rabaugart/helclock/Software/clock3/c3/color.py

import functools
from enum import Enum

class RGB(Enum):
    rot = 0
    grün = 1
    blau = 2

class Color:
    def __init__(self,r,g,b):
        self.b = bytearray([r,g,b])
    def set(self,rgb,value):
        self.b[rgb.value] = int(value) & 0xff
    def __eq__(self,o):
        if isinstance(o,Color):
            return self.b == o.b
        return False
    def __mul__(self,fac):
        nfac = max(min(float(fac),1.0),0.0)
        return Color(*list(int(i*nfac) for i in self.b))
    def copy(self):
        return Color(self.b[0],self.b[1],self.b[2])
    def __hash__(self):
        return hash(self.b.hex())
    def msg_dict(self):
        return {
            RGB.rot.name: self.b[0],
            RGB.grün.name: self.b[1],
            RGB.blau.name: self.b[2],
        }
    def serialize(self):
        return self.b.hex()
    @staticmethod
    def deserialize(bs):
        b = bytearray.fromhex(bs)
        return Color(b[0],b[1],b[2])
    def __str__(self):
        return f"C({self.b[0]},{self.b[1]},{self.b[2]})"
    def __repr__(self):
        return self.__str__()
    def __eq__(self,o):
        if isinstance(o,Color):
            return self.b == o.b
        return False


ROT = Color(255,0,0)
GRÜN = Color(0,255,0)
BLAU = Color(0,0,255)
GELB = Color(255,255,0)
WEISS = Color(255,255,255)
LILA = Color(255,0,255)
SCHWARZ = Color(0,0,0)

VORDEFINIERTE_FARBEN = [ROT,GRÜN,BLAU,LILA,GELB]

def colors_bytes(cols):
    "Wandelt Liste von Color in bytearray um"
    return functools.reduce( lambda a,b: a+b.b, cols, bytearray([]))

def filled_color_array(cols,le,fillcolor=SCHWARZ):
    "Fülle mit fillcolor bis zur Länge le auf"
    return cols + [fillcolor]*(le-len(cols))
