rabaugart/helclock/Software/clock3/c3/worte.py

from enum import Enum

W = Enum('W',"ES IST FÜNF_A ZEHN_A ZWANZIG DREI_A VIERTEL VOR NACH HALB \
ELF FÜNF_B EIN EINS ZWEI DREI_B VIER SECHS ACHT SIEBEN ZWÖLF ZEHN_B NEUN UHR".split(" "))

# Extra Worte, zusätzlich zur Uhrzeit
XW = Enum("XW","B BE SO DOM HEL RA F")

# Worte für Minuten
MIW = Enum("MIW","M1 M2 M3 M4")

TagKat = Enum("TagKat", "Normal Feiertag FamGeburtstag BekGeburtstag")

_HAS_MINUTEN = False

def zeige_minuten():
    return _HAS_MINUTEN

def aktiviere_minutenanzeige(b=True):
    global _HAS_MINUTEN
    _HAS_MINUTEN = b
